Pmitrega/Linefollower/Core/Inc/sensors.h

#ifndef __SENSORS_H
#define _SENSORS_H
#include "main.h"
#define SENSOR0_WHITE 3444
#define SENSOR1_WHITE 3355
#define SENSOR2_WHITE 3407
#define SENSOR3_WHITE 3445  
#define SENSOR4_WHITE 3444
#define SENSOR5_WHITE 3409
#define SENSOR6_WHITE 3439
#define SENSOR7_WHITE 3416

#define SENSOR0_BLACK 3688
#define SENSOR1_BLACK 3616
#define SENSOR2_BLACK 3639
#define SENSOR3_BLACK 3664  
#define SENSOR4_BLACK 3649
#define SENSOR5_BLACK 3671
#define SENSOR6_BLACK 3665
#define SENSOR7_BLACK 3615

#define HALF_ANGLE 23.0f
#define DIFF_PER_SENSOR HALF_ANGLE/4

#define SENSOR_THRE 60

#define BASE_SPEED_REMEMBER 110
int estimate_angle(uint16_t* sensors);
#endif
